szolotykh/KinisiWheels/Kinisi-100-10-M2/Center.stl

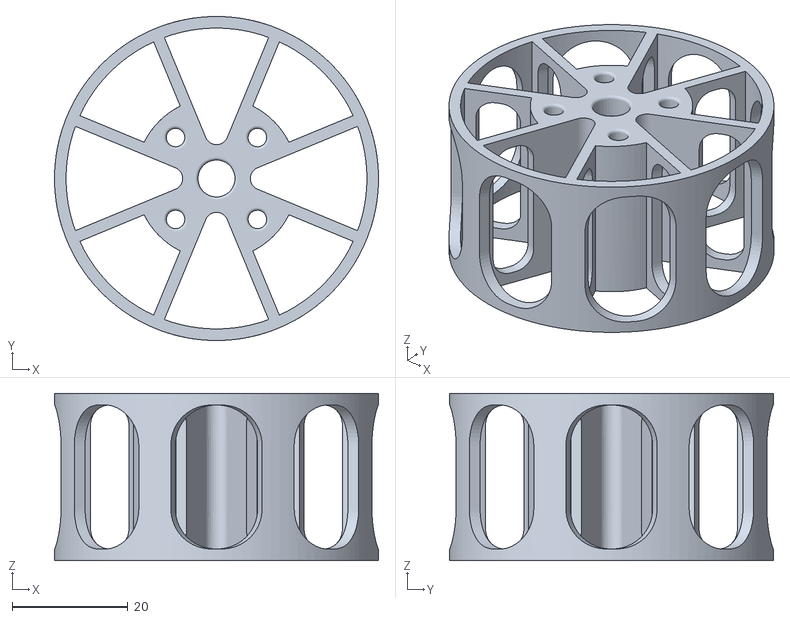
[picture p11: CAD file, 2018-06-18]
Kinisi-100-10-M2/Center.stl
56.0 x 56.0 x 28.9
