szolotykh/KinisiWheels/Kinisi-150-14-M1/Secondary beam.stl

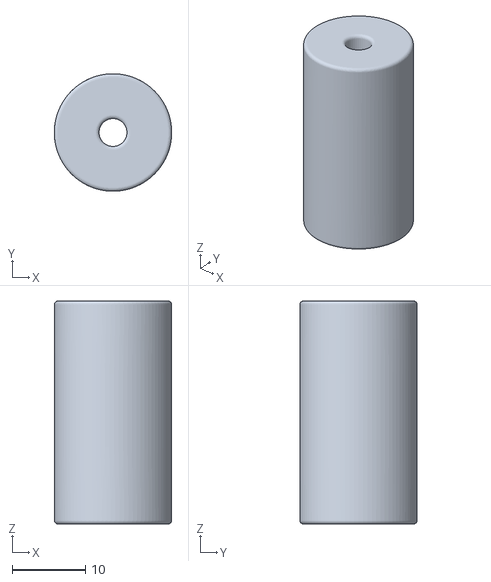
[picture p12: CAD file, 2018-07-02]
Kinisi-150-14-M1/Secondary beam.stl
16.0 x 16.0 x 30.4
